gianlucarenzi/stalker/hw/AmigaKeyboardAdapters/A500-Internal/images/A500MPU-Adapter.png

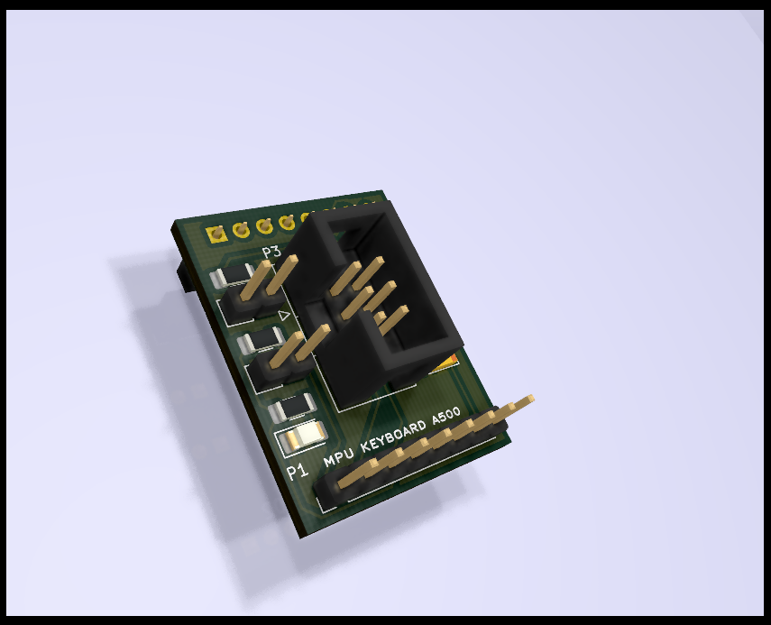
hw/AmigaKeyboardAdapters/A500-Internal/images/A500MPU-Adapter.png
