gianlucarenzi/stalker/hw/AmigaKeyboardAdapters/A600-Internal/images/A600MPU-Adapter-B.png

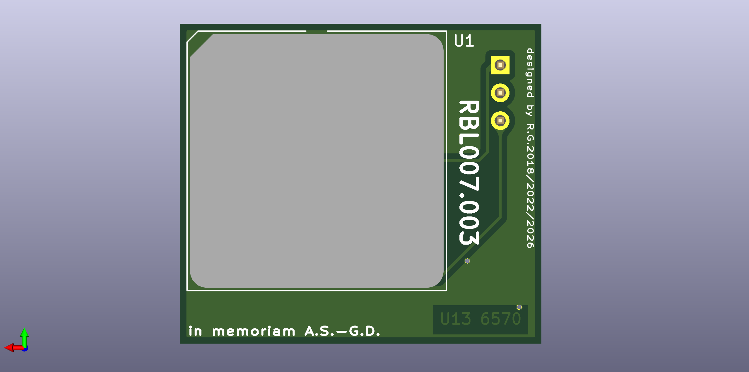
hw/AmigaKeyboardAdapters/A600-Internal/images/A600MPU-Adapter-B.png
