gianlucarenzi/stalker/hw/AmigaKeyboardAdapters/A600-Internal/images/A600MPU-Adapter-F.png

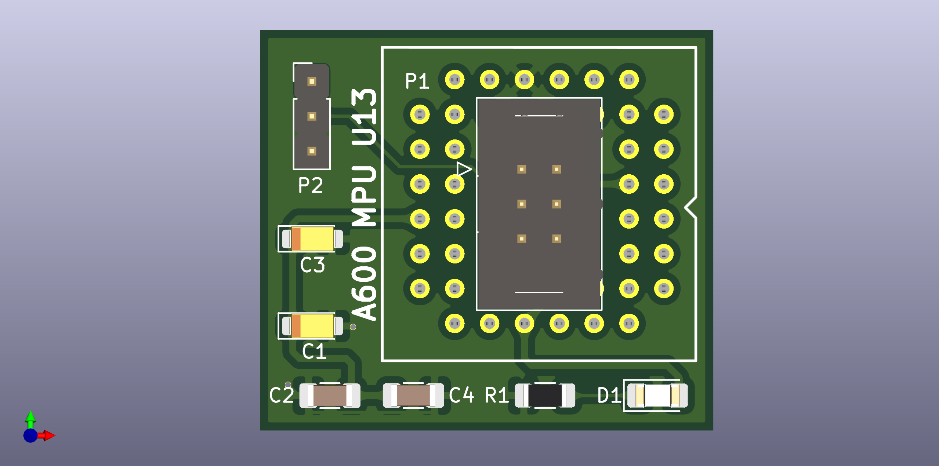
hw/AmigaKeyboardAdapters/A600-Internal/images/A600MPU-Adapter-F.png
