gianlucarenzi/stalker/hw/AmigaKeyboardAdapters/A1200-Internal/A1200MPU-Adapter-b.png

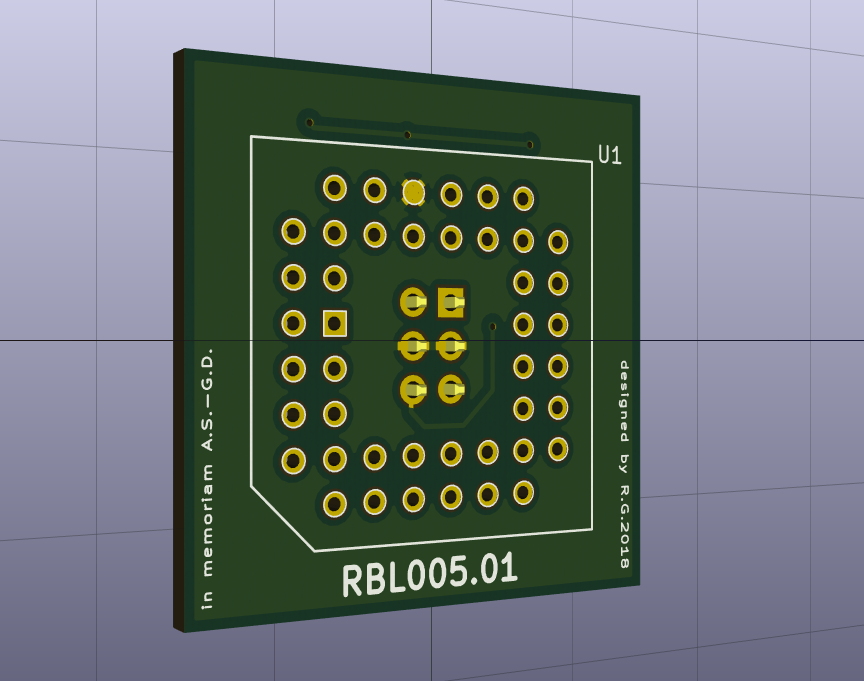
hw/AmigaKeyboardAdapters/A1200-Internal/A1200MPU-Adapter-b.png
