gianlucarenzi/stalker/hw/AmigaKeyboardAdapters/A1200-Internal/A1200MPU-Adapter-f.png

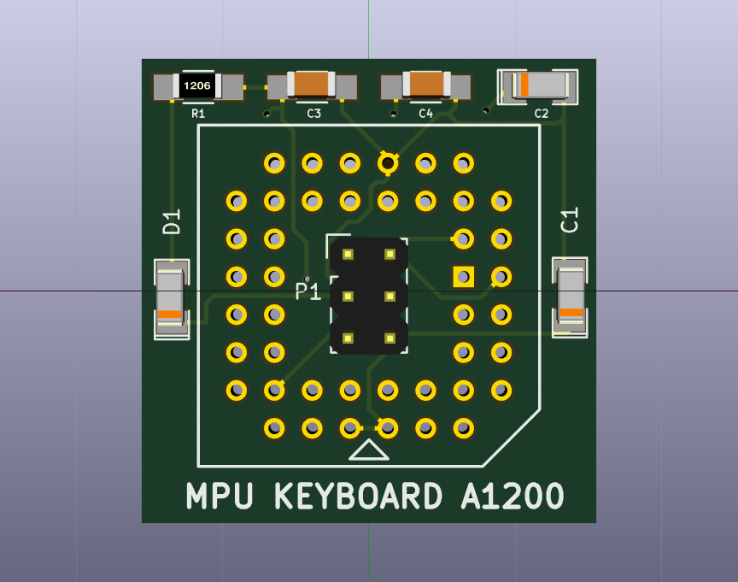
hw/AmigaKeyboardAdapters/A1200-Internal/A1200MPU-Adapter-f.png
