gianlucarenzi/stalker/timing_flow.png

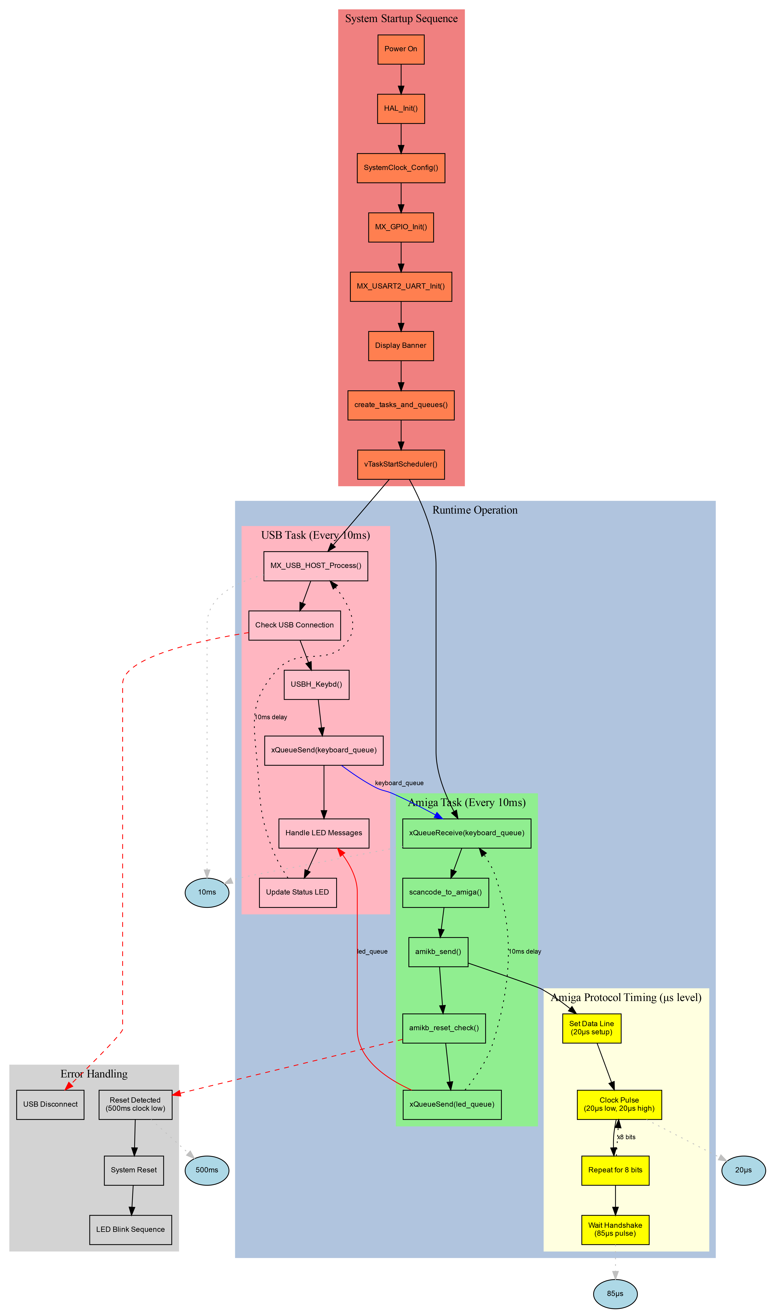
timing_flow.png
