gianlucarenzi/stalker/hw/AmigaKeyboardAdapters/StandAlone-Adapter/production/StandAlone-Adapter.ods

Id | Designator | Package | Quantity | Designation | Codice componente | Codice produttore | Descrizione
1 | U3 | LQFP-64_10x10mm_Pitch0.5mm | 1 | STM32F401RBTx | 497-18782-1-ND | STM32F401RBT6 | IC MCU 32BIT 128KB FLASH 64LQFP
2 | H4,H3,H2,H1 | 1pin | 4 | CONN_01X01 | LM1117MP-3.3/NOPBCT-ND | LM1117MP-3.3/NOPB | IC REG LINEAR 3.3V 800MA SOT223
3 | U1 | SOT-223 | 1 | AZ1117-3.3 | BSS138CT-ND | BSS138 | MOSFET N-CH 50V 220MA SOT-23
4 | TP1 | SolderWirePad_single_0-8mmDrill | 1 | GND | AE10381-ND | A-2004-3-4-LP-N-R | CONN MOD JACK 4P4C R/A UNSHLD
5 | Q3,Q2,Q1 | SOT-23 | 3 | BSS138 | ED2989-ND | USB-A1HSW6 | CONN RCPT TYPEA 4POS R/A
6 | J1 | RJ10-RECEPTACLE-Assmann-ASS-2004-3-4-LP-N-R | 1 | RJ10 | 478-1657-1-ND | TAJA106M010RNJ | CAP TANT 10UF 20% 10V 1206
7 | D1,D2,D3,D4 | LED_1206 | 4 | LED | 399-3692-1-ND | T491A226M010AT | CAP TANT 22UF 20% 10V 1206
8 | R1,R2,R6,R13 | R_1206_HandSoldering | 4 | 1.5K | 720-1803-1-ND | VJ1206Y104KXJPW1BC | CAP CER 0.1UF 16V X7R 1206
9 | R3 | R_1206_HandSoldering | 1 | 22K | 399-12968-1-ND | C1206C475K8NACAUTO | CAP CER 4.7UF 10V X8L 1206
10 | R4,R5,R7,R8,R9,R10,R11,R12,R14,R15 | R_1206_HandSoldering | 10 | 10K | P1.5KECT-ND | ERJ-8GEYJ152V | RES SMD 1.5K OHM 5% 1/4W 1206
11 | USB1 | USB_A_UP | 1 | CONN_01x04 | 541-4201-1-ND | CRCW120610K0JNEAC | RES SMD 10K OHM 5% 1/4W 1206
12 | XT1 | Crystal_HC49-4H_Vertical_3D | 1 | 8Mhz | RMCF1206JT22K0CT-ND | RMCF1206JT22K0 | RES 22K OHM 5% 1/4W 1206
13 | C6,C7,C8,C9,C3,C10,C12,C14 | C_1206_HandSoldering | 8 | 100n | 160-1166-1-ND | LTST-C150AKT | LED AMBER CLEAR SMD
14 | C5,C4 | C_1206_HandSoldering | 2 | 20p | 160-1643-1-ND | LTST-C150TBKT | LED BLUE CLEAR 1206 SMD
15 | SWDIO/CLK1,POWER1 | Pin_Header_Angled_1x04 | 2 | CONN_01X04 | 311-12ERCT-ND | RC1206JR-0712RL | RES SMD 12 OHM 5% 1/4W 1206
16 | DEBUG1,BOOT1,BOOT0 | Pin_Header_Straight_1x03 | 3 | CONN_01X03 | 631-1100-ND | FC4STCBMF8.0-BAG200 | CRYSTAL 8.0000MHZ 20PF T/H
17 | TP1/1,USB_ID1,P1,EN1 | Pin_Header_Straight_1x02 | 4 | CONN_01X02 | 1276-1661-1-ND | CL05C200JB5NNNC | CAP CER 20PF 50V C0G/NP0 0402
18 | RESET1 | SW_SPST_FSMSM_3D | 1 | SW_PUSH | 732-5394-ND | 61200621621 | CONN HEADER VERT 6POS 2.54MM
19 | AMIGA_KEYBOARD1 | Pin_Header_Angled_1x05 | 1 | CONN_01X05 | 609-3288-ND | 68001-420HLF | CONN HEADER VERT 20POS 2.54MM
20 | J2 | IDC-Header_2x03_P2.54mm_Vertical | 1 | Conn_02x03_Odd_Even | 609-3325-ND | 68016-220HLF | CONN HEADER R/A 20POS 2.54MM
21 | C13 | C_1206_HandSoldering | 1 | 4.7u | 450-1140-ND | FSMSM | SWITCH TACTILE SPST-NO 0.05A 24V
22 | R16,R17 | R_1206_HandSoldering | 2 | 12ohm
23 | C1,C11 | TantalC_SizeA_EIA-3216_HandSoldering | 2 | 10u
24 | C2 | TantalC_SizeA_EIA-3216_HandSoldering | 1 | 22u
25 | WBLOGO | amigaWorkBench1 | 1 | LOGO
26 | AMIGALOGO | amigaLogo_BW_31x12mm | 1 | LOGO
27 | GNULOGO | Symbol_GNU-GPL_SilkScreen_Small | 1 | Symbol_GNU-GPL_CopperTop_Small
