gianlucarenzi/stalker/src/amiga.c

/**
 * Amiga housekeeping as MPU.
 * Written by Gianluca Renzi R.G.
 * (C) Copyright 2019/2025 by Gianluca Renzi (RetroBitLab Tech Guy)
 * 
 * //
 * // SPDX-License-Identifier: LGPL-3.0-or-later
 *
 * License for this code: LGPLv3
 * Please refer to this license at GNU Web Site
 * https://www.gnu.org/licenses/lgpl-3.0.html
 * 
 **/
#include <string.h>
#include <stdlib.h>
#include <stdbool.h>
#include "main.h"
#include "amiga.h"
#include "debug.h"
#include "cmsis_os.h"
#include "usb_hid_keys.h"
#include "led_manager_task.h"
#include "amiga_task.h"
#include "delay_us.h"
#include "eeprom_task.h"

extern volatile reset_keypress_mode_t current_mode; // Defined in main.c

static int debuglevel = DBG_INFO;

/* KEY definitions moved to usb_hid_keys.h */


#define KEYCODE_TAB_SIZE      122

static const uint8_t scancodeamiga[KEYCODE_TAB_SIZE][2] =
{
 	// SCANCODE USB to AMIGA
 	// --------------------------------------------------------------
 	// Need the real scancode by testing all keys on a real keyboard.
 	// --------------------------------------------------------------
 	// Keycodes from: https://wiki.amigaos.net/wiki/Keymap_Library
 	// --------------------------------------------------------------
	{KEY_GRAVE_ACCENT_AND_TILDE, 0x00 }, // ~
	{KEY_1_EXCLAMATION_MARK,     0x01 }, // 1!
	{KEY_2_AT,                   0x02 }, // 2@
	{KEY_3_NUMBER_SIGN,          0x03 }, // 3#
	{KEY_4_DOLLAR,               0x04 }, // 4$
	{KEY_5_PERCENT,              0x05 }, // 5%
	{KEY_6_CARET,                0x06 }, // 6^
	{KEY_7_AMPERSAND,            0x07 }, // 7&
	{KEY_8_ASTERISK,             0x08 }, // 8*
	{KEY_9_OPARENTHESIS,         0x09 }, // 9(
	{KEY_0_CPARENTHESIS,         0x0A }, // 0)
	{KEY_MINUS_UNDERSCORE,       0x0B }, // -_
	{KEY_EQUAL_PLUS,             0x0C }, // +=
	{KEY_BACKSLASH_VERTICAL_BAR, 0x0D }, // |
	{KEY_INTERNATIONAL3,         0x0E }, // Intl 3 Yen
	{KEY_KEYPAD_0_INSERT,        0x0F }, // NUM 0
	{KEY_Q,                      0x10 }, // Q
	{KEY_W,                      0x11 }, // W
	{KEY_E,                      0x12 }, // E
	{KEY_R,                      0x13 }, // R
	{KEY_T,                      0x14 }, // T
	{KEY_Y,                      0x15 }, // Y
	{KEY_U,                      0x16 }, // U
	{KEY_I,                      0x17 }, // I
	{KEY_O,                      0x18 }, // O
	{KEY_P,                      0x19 }, // P
	{KEY_OBRACKET_AND_OBRACE,    0x1A }, // [{
	{KEY_CBRACKET_AND_CBRACE,    0x1B }, // ]}
	{KEY_INTERNATIONAL5,         0x1C }, // undefined Intl 5
	{KEY_KEYPAD_1_END,           0x1D }, // NUM 1
	{KEY_KEYPAD_2_DOWN_ARROW,    0x1E }, // NUM 2
	{KEY_KEYPAD_3_PAGEDN,        0x1F }, // NUM 3
	{KEY_A,                      0x20 }, // A
	{KEY_S,                      0x21 }, // S
	{KEY_D,                      0x22 }, // D
	{KEY_F,                      0x23 }, // F
	{KEY_G,                      0x24 }, // G
	{KEY_H,                      0x25 }, // H
	{KEY_J,                      0x26 }, // J
	{KEY_K,                      0x27 }, // K
	{KEY_L,                      0x28 }, // L
	{KEY_SEMICOLON_COLON,        0x29 }, // :;
	{KEY_SINGLE_AND_DOUBLE_QUOTE,0x2A }, // "'
	{KEY_INTERNATIONAL1,         0x2B }, // undefined Intl 1
	{KEY_INTERNATIONAL4,         0x2C }, // undefined Intl 4
	{KEY_KEYPAD_4_LEFT_ARROW,    0x2D }, // NUM 4
	{KEY_KEYPAD_5,               0x2E }, // NUM 5
	{KEY_KEYPAD_6_RIGHT_ARROW,   0x2F }, // NUM 6
	{KEY_INTERNATIONAL2,         0x30 }, // <SHIFT> international? Intl 2
	{KEY_Z,                      0x31 }, // Z
	{KEY_X,                      0x32 }, // X
	{KEY_C,                      0x33 }, // C
	{KEY_V,                      0x34 }, // V
	{KEY_B,                      0x35 }, // B
	{KEY_N,                      0x36 }, // N
	{KEY_M,                      0x37 }, // M
	{KEY_COMMA_AND_LESS,         0x38 }, // <,
	{KEY_DOT_GREATER,            0x39 }, // >.
	{KEY_SLASH_QUESTION,         0x3A }, // ?/
	{KEY_INTERNATIONAL6,         0x3B }, // undefined Intl 6
	{KEY_KEYPAD_DECIMAL_SEPARATOR_DELETE, 0x3C }, // KEYPAD '.'
	{KEY_KEYPAD_7_HOME,          0x3D }, // NUM 7
	{KEY_KEYPAD_8_UP_ARROW,      0x3E }, // NUM 8
	{KEY_KEYPAD_9_PAGEUP,        0x3F }, // NUM 9
	{KEY_SPACEBAR,               0x40 }, // SPACE
	{KEY_BACKSPACE,              0x41 }, // BACKSPACE
	{KEY_TAB,                    0x42 }, // TAB
	{KEY_ENTER,                  0x43 }, // ENTER
	{KEY_RETURN,                 0x43 }, // RETURN
	{KEY_KEYPAD_ENTER,           0x44 }, // NUM Enter
	{KEY_ESCAPE,                 0x45 }, // ESC
	{KEY_DELETE,                 0x46 }, // DEL
	{KEY_INSERT,                 0x47 }, // INS (usually undefined)
	{KEY_PAGEUP,                 0x48 }, // PAGEUP (usually undefined)
	{KEY_PAGEDOWN,               0x49 }, // PAGEDOWN (usually undefined)
	{KEY_KEYPAD_MINUS,           0x4A }, // NUM -
	{KEY_F11,                    0x4B }, // F11
	{KEY_UPARROW,                0x4C }, // CURSOR U
	{KEY_DOWNARROW,              0x4D }, // CURSOR D
	{KEY_RIGHTARROW,             0x4E }, // CURSOR R
	{KEY_LEFTARROW,              0x4F }, // CURSOR L
	{KEY_F1,                     0x50 }, // F1
	{KEY_F2,                     0x51 }, // F2
	{KEY_F3,                     0x52 }, // F3
	{KEY_F4,                     0x53 }, // F4
	{KEY_F5,                     0x54 }, // F5
	{KEY_F6,                     0x55 }, // F6
	{KEY_F7,                     0x56 }, // F7
	{KEY_F8,                     0x57 }, // F8
	{KEY_F9,                     0x58 }, // F9
	{KEY_F10,                    0x59 }, // F10
	{KEY_KEYPAD_OPARENTHESIS,    0x5A }, // NUM (
	{KEY_KEYPAD_CPARENTHESIS,    0x5B }, // NUM )
	{KEY_KEYPAD_SLASH,           0x5C }, // /
	{KEY_KEYPAD_ASTERIKS,        0x5D }, // NUM *
	{KEY_KEYPAD_PLUS,            0x5E }, // NUM +
	{KEY_HELP,                   0x5F }, // HELP
	{KEY_SCROLL_LOCK,            0x5F }, // HELP (Mapped to ScrollLock?)
	{KEY_APPLICATION,            0x5F }, // APP - HELP (Mapped to Key Application?)
	{KEY_LEFTSHIFT,              0x60 }, // LSHIFT
	{KEY_RIGHTSHIFT,             0x61 }, // RSHIFT
	{KEY_CAPS_LOCK,              0x62 }, // CAPS
	{KEY_LEFTCONTROL,            0x63 }, // LCTRL
	{KEY_RIGHTCONTROL,           0x63 }, // RCTRL
	{KEY_LEFTALT,                0x64 }, // LALT
	{KEY_RIGHTALT,               0x65 }, // RALT
	{KEY_LEFT_GUI,               0x66 }, // LWIN
	{KEY_RIGHT_GUI,              0x67 }, // RWIN
	{KEY_LMOUSE_BUTTON,          0x68 }, // LMOUSE BUTTON
	{KEY_RMOUSE_BUTTON,          0x69 }, // RMOUSE BUTTON
	{KEY_MMOUSE_BUTTON,          0x6A }, // MMOUSE BUTTON
	{KEY_MENU,                   0x6B }, // MENU, GUI, COMPOSE (mappable to RAmiga in Firmware)
	{KEY_KEYPAD_COMMA,           0x6C }, // Brazil NP . (named "Keypad ," in USB specs)
	{KEY_PRINTSCREEN,            0x6D }, // PrintScreen/SysReq (mappable to Help in Firmware)
	{KEY_SYSREQ,                 0x6E }, // BREAK
	{KEY_F12,                    0x6F }, // F12
	{KEY_HOME,                   0x70 }, // HOME
	{KEY_END1,                   0x71 }, // END
	{KEY_STOP,                   0x72 }, // STOP/CD32 Blue Stop, CDTV Stop, Port 0 Blue
	{KEY_PAUSE,                  0x73 }, // Play/Pause CD32 Grey Play/Pause CDTV Play/Pause Port 0 Blue
	{KEY_VOLUME_UP,              0x74 }, // Prev Track CDTV << REV
	{KEY_VOLUME_DOWN,            0x75 }, // Next Track CDTV >> FF
};

static const uint8_t asciiscancode[KEYCODE_TAB_SIZE][2] =
{
	{KEY_GRAVE_ACCENT_AND_TILDE, '~' }, // ~
	{KEY_1_EXCLAMATION_MARK,     '!' }, // 1!
	{KEY_2_AT,                   '@' }, // 2@
	{KEY_3_NUMBER_SIGN,          '#' }, // 3#
	{KEY_4_DOLLAR,               '$' }, // 4$
	{KEY_5_PERCENT,              '%' }, // 5%
	{KEY_6_CARET,                '^' }, // 6^
	{KEY_7_AMPERSAND,            '&' }, // 7&
	{KEY_8_ASTERISK,             '*' }, // 8*
	{KEY_9_OPARENTHESIS,         '(' }, // 9(
	{KEY_0_CPARENTHESIS,         ')' }, // 0)
	{KEY_MINUS_UNDERSCORE,       '-' }, // -_
	{KEY_EQUAL_PLUS,             '+' }, // +=
	{KEY_BACKSLASH_VERTICAL_BAR, '|' }, // |
	{KEY_NONE,                   '-' }, // @
	{KEY_KEYPAD_0_INSERT,        '0' }, // NUM 0
	{KEY_Q,                      'Q' }, // Q
	{KEY_W,                      'W' }, // W
	{KEY_E,                      'E' }, // E
	{KEY_R,                      'R' }, // R
	{KEY_T,                      'T' }, // T
	{KEY_Y,                      'Y' }, // Y
	{KEY_U,                      'U' }, // U
	{KEY_I,                      'I' }, // I
	{KEY_O,                      'O' }, // O
	{KEY_P,                      'P' }, // P
	{KEY_OBRACKET_AND_OBRACE,    '{' }, // [{
	{KEY_CBRACKET_AND_CBRACE,    '}' }, // ]}
	{KEY_SPACEBAR,               ' ' }, // SPACE
	{KEY_KEYPAD_1_END,           '1' }, // NUM 1
	{KEY_KEYPAD_2_DOWN_ARROW,    '2' }, // NUM 2
	{KEY_KEYPAD_3_PAGEDN,        '3' }, // NUM 3
	{KEY_A,                      'A' }, // A
	{KEY_S,                      'S' }, // S
	{KEY_D,                      'D' }, // D
	{KEY_F,                      'F' }, // F
	{KEY_G,                      'G' }, // G
	{KEY_H,                      'H' }, // H
	{KEY_J,                      'J' }, // J
	{KEY_K,                      'K' }, // K
	{KEY_L,                      'L' }, // L
	{KEY_SEMICOLON_COLON,        ':' }, // :;
	{KEY_SINGLE_AND_DOUBLE_QUOTE,'"' }, // "'
	{KEY_ENTER,                  '\n'}, // <RET> international?
	{KEY_KEYPAD_4_LEFT_ARROW,    '4' }, // NUM 4
	{KEY_KEYPAD_5,               '5' }, // NUM 5
	{KEY_KEYPAD_6_RIGHT_ARROW,   '6' }, // NUM 6
	{KEY_INTERNATIONAL2,         '-' }, // <SHIFT> international?
	{KEY_Z,                      'Z' }, // Z
	{KEY_X,                      'X' }, // X
	{KEY_C,                      'C' }, // C
	{KEY_V,                      'V' }, // V
	{KEY_B,                      'B' }, // B
	{KEY_N,                      'N' }, // N
	{KEY_M,                      'M' }, // M
	{KEY_COMMA_AND_LESS,         '<' }, // <,
	{KEY_KEYPAD_COMMA,           ',' }, // NUM ,
	{KEY_DOT_GREATER,            '>' }, // >.
	{KEY_SLASH_QUESTION,         '?' }, // ?/
	{KEY_KEYPAD_7_HOME,          '7' }, // NUM 7
	{KEY_KEYPAD_8_UP_ARROW,      '8' }, // NUM 8
	{KEY_KEYPAD_9_PAGEUP,        '9' }, // NUM 9
	{KEY_SPACEBAR,               ' ' }, // SPACE
	{KEY_BACKSPACE,              '\r'}, // BACKSPACE
	{KEY_TAB,                    '\t'}, // TAB
	{KEY_KEYPAD_ENTER,           '\n'}, // ENTER
	{KEY_RETURN,                 '\n'}, // RETURN
	{KEY_ESCAPE,                 '-' }, // ESC
	{KEY_DELETE,                 '\r'}, // DEL
	{KEY_KEYPAD_MINUS,           '-' }, // NUM -
	{KEY_KEYPAD_SLASH,           '/' }, // /
	{KEY_KEYPAD_ASTERIKS,        '*' }, // NUM *
	{KEY_KEYPAD_PLUS,            '+' }, // NUM +
	{KEY_HELP,                   'h' }, // HELP
	{KEY_APPLICATION,            'h' }, // APP - HELP
	{KEY_NONE,                   '(' }, // (
	{KEY_NONE,                   ')' }, // )
	{KEY_NONE,                   ' ' }, // SPARE
	{KEY_NONE,                   ' ' }, // SPARE
	{KEY_NONE,                   ' ' }, // SPARE
	{KEY_NONE,                   ' ' }, // SPARE
	{KEY_NONE,                   ' ' }, // SPARE
	{KEY_NONE,                   ' ' }, // SPARE
	{KEY_UPARROW,                ' ' }, // CURSOR U
	{KEY_DOWNARROW,              ' ' }, // CURSOR D
	{KEY_RIGHTARROW,             ' ' }, // CURSOR R
	{KEY_LEFTARROW,              ' ' }, // CURSOR L
	{KEY_F1,                     ' ' }, // F1
	{KEY_F2,                     ' ' }, // F2
	{KEY_F3,                     ' ' }, // F3
	{KEY_F4,                     ' ' }, // F4
	{KEY_F5,                     ' ' }, // F5
	{KEY_F6,                     ' ' }, // F6
	{KEY_F7,                     ' ' }, // F7
	{KEY_F8,                     ' ' }, // F8
	{KEY_F9,                     ' ' }, // F9
	{KEY_F10,                    ' ' }, // F10
	{KEY_LEFTSHIFT,              ' ' }, // LSHIFT
	{KEY_RIGHTSHIFT,             ' ' }, // RSHIFT
	{KEY_LOCKING_CAPS_LOCK,      ' ' }, // CAPS
	{KEY_LEFTCONTROL,            ' ' }, // LCTRL
	{KEY_LEFTALT,                ' ' }, // LALT
	{KEY_RIGHTALT,               ' ' }, // RALT
	{KEY_LEFT_GUI,               ' ' }, // LWIN
	{KEY_RIGHT_GUI,              ' ' }, // RWIN
	{KEY_NONE,                   ' ' }, // STUB
	{KEY_NONE,                   ' ' }, // STUB
	{KEY_NONE,                   ' ' }, // STUB
	{KEY_NONE,                   ' ' }, // STUB
	{KEY_NONE,                   ' ' }, // STUB
	{KEY_NONE,                   ' ' }, // STUB
	{KEY_NONE,                   ' ' }, // STUB
	{KEY_NONE,                   ' ' }, // STUB
	{KEY_NONE,                   ' ' }, // STUB
	{KEY_NONE,                   ' ' }, // STUB
	{KEY_NONE,                   ' ' }, // STUB
	{KEY_NONE,                   ' ' }, // STUB
	{KEY_NONE,                   ' ' }, // STUB
	{KEY_NONE,                   ' ' }, // STUB
	{KEY_NONE,                   ' ' }, // STUB
	{KEY_NONE,                   ' ' }, // STUB
	{KEY_NONE,                   ' ' }, // STUB
};


/**
	The keyboard transmits 8-bit data words serially to the main unit. Before
	the transmission starts, both KCLK and KDAT are high.  The keyboard starts
	the transmission by putting out the first data bit (on KDAT), followed by
	a pulse on KCLK (low then high); then it puts out the second data bit and
	pulses KCLK until all eight data bits have been sent.  After the end of
	the last KCLK pulse, the keyboard pulls KDAT high again.

	When the computer has received the eighth bit, it must pulse KDAT low for
	at least 1 (one) microsecond, as a handshake signal to the keyboard.  The
	handshake detection on the keyboard end will typically use a hardware
	latch.  The keyboard must be able to detect pulses greater than or equal
	to 1 microsecond.  Software MUST pulse the line low for 85 microseconds to
	ensure compatibility with all keyboard models.

	All codes transmitted to the computer are rotated one bit before
	transmission.  The transmitted order is therefore 6-5-4-3-2-1-0-7. The
	reason for this is to transmit the  up/down flag  last, in order to cause
	a key-up code to be transmitted in case the keyboard is forced to restore
	 lost sync  (explained in more detail below).

	The KDAT line is active low; that is, a high level (+5V) is interpreted as
	0, and a low level (0V) is interpreted as 1.

				 _____   ___   ___   ___   ___   ___   ___   ___   _________
			KCLK      \_/   \_/   \_/   \_/   \_/   \_/   \_/   \_/
				 ___________________________________________________________
			KDAT    \_____X_____X_____X_____X_____X_____X_____X_____/
					  (6)   (5)   (4)   (3)   (2)   (1)   (0)   (7)

					 First                                     Last
					 sent                                      sent

	The keyboard processor sets the KDAT line about 20 microseconds before it
	pulls KCLK low.  KCLK stays low for about 20 microseconds, then goes high
	again.  The processor waits another 20 microseconds before changing KDAT.

	Therefore, the bit rate during transmission is about 60 microseconds per
	bit, or 17 kbits/sec.
	*
	*
	*
	*
	*
	*
	* Is this LookUpTable needed for translating from ascii to internal keycode?


			Row 5   Row 4   Row 3   Row 2   Row 1   Row 0
	Column    (Bit 7) (Bit 6) (Bit 5) (Bit 4) (Bit 3) (Bit 2)
		   +-------+-------+-------+-------+-------+-------+
	 15    |(spare)|(spare)|(spare)|(spare)|(spare)|(spare)|
	(PD.7) |       |       |       |       |       |       |
		   | (0E)  | (1C)  | (2C)  | (47)  | (48)  | (49)  |
		   +-------+-------+-------+-------+-------+-------+
	 14    |   *   |<SHIFT>| CAPS  |  TAB  |   ~   |  ESC  |
	(PD.6) |note 1 |note 2 | LOCK  |       |   `   |       |
		   | (5D)  | (30)  | (62)  | (42)  | (00)  | (45)  |
		   +-------+-------+-------+-------+-------+-------+
	 13    |   +   |   Z   |   A   |   Q   |   !   |   (   |
	(PD.5) |note 1 |       |       |       |   1   |note 1 |
		   | (5E)  | (31)  | (20)  | (10)  | (01)  | (5A)  |
		   +-------+-------+-------+-------+-------+-------+
	 12    |  9    |   X   |   S   |   W   |   @   |  F1   |
	(PD.4) |note 3 |       |       |       |   2   |       |
		   | (3F)  | (32)  | (21)  | (11)  | (02)  | (50)  |
		   +-------+-------+-------+-------+-------+-------+
	 11    |  6    |   C   |   D   |   E   |   #   |  F2   |
	(PD.3) |note 3 |       |       |       |   3   |       |
		   | (2F)  | (33)  | (22)  | (12)  | (03)  | (51)  |
		   +-------+-------+-------+-------+-------+-------+
	 10    |  3    |   V   |   F   |   R   |   $   |  F3   |
	(PD.2) |note 3 |       |       |       |   4   |       |
		   | (1F)  | (34)  | (23)  | (13)  | (04)  | (52)  |
		   +-------+-------+-------+-------+-------+-------+
	  9    |  .    |   B   |   G   |   T   |   %   |  F4   |
	(PD.1) |note 3 |       |       |       |   5   |       |
		   | (3C)  | (35)  | (24)  | (14)  | (05)  | (53)  |
		   +-------+-------+-------+-------+-------+-------+
	  8    |  8    |   N   |   H   |   Y   |   ^   |  F5   |
	(PD.0) |note 3 |       |       |       |   6   |       |
		   | (3E)  | (36)  | (25)  | (15)  | (06)  | (54)  |
		   +-------+-------+-------+-------+-------+-------+
	  7    |  5    |   M   |   J   |   U   |   &   |   )   |
	(PC.7) |note 3 |       |       |       |   7   |note 1 |
		   | (2E)  | (37)  | (26)  | (16)  | (07)  | (5B)  |
		   +-------+-------+-------+-------+-------+-------+
	  6    |  2    |   <   |   K   |   I   |   *   |  F6   |
	(PC.6) |note 3 |   ,   |       |       |   8   |       |
		   | (1E)  | (38)  | (27)  | (17)  | (08)  | (55)  |
		   +-------+-------+-------+-------+-------+-------+
	  5    | ENTER |   >   |   L   |   O   |   (   |   /   |
	(PC.5) |note 3 |   .   |       |       |   9   |note 1 |
		   | (43)  | (39)  | (28)  | (18)  | (09)  | (5C)  |
		   +-------+-------+-------+-------+-------+-------+
	  4    |  7    |   ?   |   :   |   P   |   )   |  F7   |
	(PC.4) |note 3 |   /   |   ;   |       |   0   |       |
		   | (3D)  | (3A)  | (29)  | (19)  | (0A)  | (56)  |
		   +-------+-------+-------+-------+-------+-------+
	  3    |  4    |(spare)|   "   |   {   |   _   |  F8   |
	(PC.3) |note 3 |       |   '   |   [   |   -   |       |
		   | (2D)  | (3B)  | (2A)  | (1A)  | (0B)  | (57)  |
		   +-------+-------+-------+-------+-------+-------+
	  2    |  1    | SPACE | <RET> |   }   |   +   |  F9   |
	(PC.2) |note 3 |  BAR  |note 2 |   ]   |   =   |       |
		   | (1D)  | (40)  | (2B)  | (1B)  | (0C)  | (58)  |
		   +-------+-------+-------+-------+-------+-------+
	  1    |  0    | BACK  |  DEL  |RETURN |   |   |  F10  |
	(PC.1) |note 3 | SPACE |       |       |   \   |       |
		   | (0F)  | (41)  | (46)  | (44)  | (0D)  | (59)  |
		   +-------+-------+-------+-------+-------+-------+
	  0    |  -    | CURS  | CURS  | CURS  | CURS  | HELP  |
	(PC.0) |note 3 | DOWN  | RIGHT | LEFT  |  UP   |       |
		   | (4A)  | (4D)  | (4E)  | (4F)  | (4C)  | (5F)  |
		   +-------+-------+-------+-------+-------+-------+

	note 1: A500, A2000 and A3000 keyboards only (numeric pad )
	note 2: International keyboards only (these keys are cutouts of the
		   larger key on the US ASCII version.)  The key that generates
		   $30 is cut out of the left Shift key.  Key $2B is cut out of
		   return.  These keys are labeled with country-specific markings.
	note 3: Numeric pad.


	The following table shows which keys are independently readable.  These
	keys never generate ghosts or phantoms.


		(Bit 6) (Bit 5) (Bit 4) (Bit 3) (Bit 2) (Bit 1) (Bit 0)
	   +-------+-------+-------+-------+-------+-------+-------+
	   | LEFT  | LEFT  | LEFT  | CTRL  | RIGHT | RIGHT | RIGHT |
	   | AMIGA | ALT   | SHIFT |       | AMIGA |  ALT  | SHIFT |
	   | (66)  | (64)  | (60)  | (63)  | (67)  | (65)  | (61)  |
	   +-------+-------+-------+-------+-------+-------+-------+

	About Hard Reset.
	-----------------
	Hard Reset happens after  Reset Warning . Valid for all keyboards
	except the Amiga 500.

	The keyboard Hard Resets the Amiga by pulling KCLK low and starting a 500
	millisecond timer.   When one or more of the keys is released and 500
	milliseconds have passed, the keyboard will release KCLK. 500 milliseconds
	is the minimum time KCLK must be held low.  The maximum KCLK time depends
	on how long the user holds the three  reset keys  down.  Circuitry on the
	Amiga motherboard detects the 500 millisecond KCLK pulse.

	After releasing KCLK, the keyboard jumps to its start-up code (internal
	RESET).  This will initialize the keyboard in the same way as cold
	power-on .

 **/

typedef enum {
	DAT_OUTPUT = 0,
	DAT_INPUT,
} kbd_dir;

static unsigned char prev_keycode = 0xff;
static unsigned char capslk = 0;
static unsigned char numlk = 0;
static unsigned char scrolllk = 0;

static void amikb_direction(kbd_dir dir);
led_status_t amikb_send(uint8_t code, int press, int use_OS);

/**
 * @brief  Converts a USB HID scancode to an Amiga scancode.
 * @param  lkey: The USB HID scancode.
 * @retval The corresponding Amiga scancode.
 **/
uint8_t scancode_to_amiga(uint8_t lkey)
{
	uint8_t i = 0, keyvalue = lkey;
	DBG_V("Enter with 0x%02x lkey ScanCode\r\n", lkey);

	for (i = 0; i < KEYCODE_TAB_SIZE; i++)
	{
		DBG_N("SCANCODE: 0x%02x - AMIGA: 0x%02x\r\n",
			scancodeamiga[i][0], scancodeamiga[i][1]);
		if (lkey == scancodeamiga[i][0])
		{
			keyvalue = scancodeamiga[i][1];
			break;
		}
	}

	DBG_V("Exit with: 0x%02x Amiga ScanCode\r\n", keyvalue);
	return keyvalue;
}

/**
 * @brief  Converts an ASCII character to a USB HID scancode.
 * @param  ascii: The ASCII character.
 * @retval The corresponding USB HID scancode.
 **/
uint8_t ascii_to_scancode(uint8_t ascii)
{
	uint8_t i = 0, keyvalue = ascii;
	DBG_V("Enter with '%c' 0x%02x ASCII\r\n", ascii, ascii);

	for (i = 0; i < KEYCODE_TAB_SIZE; i++)
	{
		if (ascii == asciiscancode[i][1])
		{
			keyvalue = asciiscancode[i][0];
			break;
		}
	}

	DBG_V("Exit with: 0x%02x ScanCode\r\n", keyvalue);
	return keyvalue;
}

/**
 * @brief  Initializes the Amiga keyboard.
 * @retval None
 **/
void amikb_startup(int use_OS)
{
	uint8_t AMIGA_INITPOWER = 0xFD; //11111101
	uint8_t AMIGA_TERMPOWER = 0xFE; //11111110

	DBG_V("Enter\r\n");

	// De-assert nRESET for Amiga...
	amikb_reset(use_OS);

	amikb_direction(DAT_OUTPUT); // Default

	if (use_OS)
	{
		osDelay(RESET_TIMEOUT_MS * 2);
	}
	else
	{
		HAL_Delay(RESET_TIMEOUT_MS * 2);              // wait for sync
	}
	amikb_send((uint8_t) AMIGA_INITPOWER, 0, use_OS); // send "initiate power-up"
	udelay(200);
	amikb_send((uint8_t) AMIGA_TERMPOWER, 0, use_OS); // send "terminate power-up"

	DBG_V("Exit\r\n");
}

static int keyboard_is_present = 0;

/**
 * @brief  Sets the keyboard presence status.
 * @param  isready: 1 if the keyboard is present, 0 otherwise.
 * @retval None
 **/
void amikb_ready(int isready)
{
	keyboard_is_present = isready;
}

/**
 * @brief  Initializes the GPIO pins for the Amiga keyboard.
 * @retval None
 **/
void amikb_gpio_init(void)
{
	GPIO_InitTypeDef GPIO_InitStruct;

	DBG_N("Enter\r\n");

	/* GPIO Port C Clock Enable */
	__HAL_RCC_GPIOC_CLK_ENABLE();

	/*Configure GPIO pin Output Level */
	HAL_GPIO_WritePin(GPIOC,
		KBD_CLOCK_Pin |
		KBD_DATA_Pin  |
		KBD_RESET_Pin, GPIO_PIN_SET);

	/*Configure GPIO pins : KBD_CLOCK_Pin KBD_DATA_Pin KBD_RESET_Pin */
	GPIO_InitStruct.Pin = KBD_CLOCK_Pin |KBD_DATA_Pin | KBD_RESET_Pin;
	GPIO_InitStruct.Mode = GPIO_MODE_OUTPUT_PP;
	GPIO_InitStruct.Pull = GPIO_NOPULL;
	GPIO_InitStruct.Speed = GPIO_SPEED_FREQ_LOW;
	HAL_GPIO_Init(GPIOC, &GPIO_InitStruct);

	// Lasciamo l'Amiga in RESET finche' non parte la macchina a stati
	HAL_GPIO_WritePin(GPIOC, KBD_RESET_Pin, GPIO_PIN_RESET); // Clear KBD_RESET pin

	DBG_N("Exit\r\n");
}

/**
 * @brief  Sets the direction of the keyboard data and clock lines.
 * @param  dir: The direction of the lines (DAT_INPUT or DAT_OUTPUT).
 * @retval None
 **/
static void amikb_direction(kbd_dir dir)
{
	GPIO_InitTypeDef GPIO_InitStruct;

	DBG_N("Enter with: %d\r\n", dir);
	/*Configure GPIO KBD_DAT, GPIO KBD_CLOCK as inputs and KBD_RESET as output */
	GPIO_InitStruct.Pin = KBD_CLOCK_Pin |KBD_DATA_Pin;
	GPIO_InitStruct.Speed = GPIO_SPEED_FREQ_LOW;
	switch (dir)
	{
		case DAT_INPUT:
			GPIO_InitStruct.Mode = GPIO_MODE_INPUT;
			GPIO_InitStruct.Pull = GPIO_PULLUP;
			break;

		default:
		case DAT_OUTPUT:
			GPIO_InitStruct.Mode = GPIO_MODE_OUTPUT_PP;
			GPIO_InitStruct.Pull = GPIO_NOPULL;
			break;
	}
	HAL_GPIO_Init(GPIOC, &GPIO_InitStruct);

	/* Now configure KBD_RESET_Pin as output */
	GPIO_InitStruct.Pin = KBD_RESET_Pin;
	GPIO_InitStruct.Mode = GPIO_MODE_OUTPUT_PP;
	GPIO_InitStruct.Pull = GPIO_NOPULL;
	GPIO_InitStruct.Speed = GPIO_SPEED_FREQ_LOW;
	HAL_GPIO_Init(GPIOC, &GPIO_InitStruct);

	DBG_N("Exit\r\n");
}

/**
 * @brief  Sends a keycode to the Amiga.
 * @param  keycode: The Amiga scancode to send.
 * @param  press: 1 if the key is pressed, 0 if it is released.
 * @retval The LED status.
 **/
led_status_t amikb_send(uint8_t keycode, int press, int use_OS)
{
	int i;
	led_status_t rval = NO_LED;

	DBG_V("Amiga Keycode 0x%02x - %s\r\n", keycode, press ? "PRESSED" : "RELEASED");
	if (keycode == 0x62 || keycode == 0x68 || keycode == 0x1c) // Caps Lock, Num Lock or Scroll Lock Pressed or Released
	{
		// caps lock doesn't get a key release event when the key is released
		// but rather when the caps lock is toggled off again
		// But what about num lock?

		switch (keycode)
		{
			case 0x62: // CAPS LOCK LED
				if (!capslk)
				{
					if (press)
					{
						DBG_V("### SEND TURN-ON CAPS LOCK LED. ALL UPPERCASE FROM NOW ###\r\n");
						rval = LED_CAPS_LOCK_ON;
						prev_keycode = 0;
						break;
					}
					else
					{
						DBG_V("### IGNORING RELEASE FOR CAPS LOCK ###\n\r");
						// Toggle for next time press
						capslk = 1;
						prev_keycode = 0;
						return NO_LED;
					}
				}
				else
				{
					if (press)
					{
						DBG_V("### IGNORING PRESS FOR CAPS LOCK. IT WAS ALREADY PRESSED ###\r\n");
						prev_keycode = 0;
						return NO_LED;
					}
					else
					{
						DBG_V("### SEND TURN-OFF CAPS LOCK LED. ALL LOWERCASE FROM NOW ###\r\n");
						capslk = 0;
						rval = LED_CAPS_LOCK_OFF;
						prev_keycode = 0;
						break;
					}
				}
				break;
			case 0x68: // NUM LOCK LED
				if (!numlk)
				{
					if (press)
					{
						DBG_V("### SEND TURN-ON NUM LOCK LED. NUMERIC KEYPAD LOCKED FROM NOW ###\r\n");
						rval = LED_NUM_LOCK_ON;
						prev_keycode = 0;
						break;
					}
					else
					{
						DBG_V("### IGNORING RELEASE FOR NUM LOCK ###\n\r");
						// Toggle for next time press
						numlk = 1;
						prev_keycode = 0;
						return NO_LED;
					}
				}
				else
				{
					if (press)
					{
						DBG_V("### IGNORING PRESS FOR NUM LOCK. IT WAS ALREADY PRESSED ###\r\n");
						prev_keycode = 0;
						return NO_LED;
					}
					else
					{
						DBG_V("### SEND TURN-OFF NUM LOCK LED. NUMERIC KEYPAD UNLOCKED FROM NOW ###\r\n");
						numlk = 0;
						rval = LED_NUM_LOCK_OFF;
						prev_keycode = 0;
						break;
					}
				}
				break;
			case 0x1c: // SCROLL LOCK LED
				if (!scrolllk)
				{
					if (press)
					{
						DBG_V("### SEND TURN-ON SCROLL LOCK LED. SCROLL IS LOCKED FROM NOW ###\r\n");
						rval = LED_SCROLL_LOCK_ON;
						prev_keycode = 0;
						break;
					}
					else
					{
						DBG_V("### IGNORING RELEASE FOR SCROLL LOCK ###\n\r");
						// Toggle for next time press
						scrolllk = 1;
						prev_keycode = 0;
						return NO_LED;
					}
				}
				else
				{
					if (press)
					{
						DBG_V("### IGNORING PRESS FOR SCROLL LOCK. IT WAS ALREADY PRESSED ###\r\n");
						prev_keycode = 0;
						return NO_LED;
					}
					else
					{
						DBG_V("### SEND TURN-OFF SCROLL LOCK LED. SCROLL IS UNLOCKED FROM NOW ###\r\n");
						scrolllk = 0;
						rval = LED_SCROLL_LOCK_OFF;
						prev_keycode = 0;
						break;
					}
				}
				break;
			default:
				{
					DBG_V("NUMLOCK %d - CAPSLOCK %d - SCROLLLOCK %d - PRESSED: %d\r\n",
						numlk, capslk, scrolllk, press);
					return NO_LED;
				}
				break;
		}
	}

	// keycode bit transfer order: 6 5 4 3 2 1 0 7 (7 is pressed flag)
	keycode = (keycode << 1) | (~press & 1);
	if (keycode == prev_keycode)
	{
		DBG_N("NO SENDING THE SAME KEYCODE TWO TIMES IN A ROW\r\n");
		return NO_LED;
	}

	prev_keycode = keycode;

	// Set direction DAT & CLOCK as output to ensure the correct
	// movement of the edges (CLK and DAT)
	amikb_direction(DAT_OUTPUT);

	// make sure we don't pulse the lines while grabbing control
	// by first reinstating the pullups before changing direction
	HAL_GPIO_WritePin(GPIOC, KBD_DATA_Pin, GPIO_PIN_SET); // Normally KBD_DATA pin is HIGH

	// pulse the data line and wait for about 100us
	HAL_GPIO_WritePin(GPIOC, KBD_DATA_Pin, GPIO_PIN_RESET); // KBD_DATA pin is LOW
	udelay(20);
	HAL_GPIO_WritePin(GPIOC, KBD_DATA_Pin, GPIO_PIN_SET); // KBD_DATA pin is HIGH
	udelay(100);

	// Send byte to LED manager for visualization
	extern osMessageQueueId_t ledManagerQueueHandle;
	if (ledManagerQueueHandle != NULL)
	{
		led_manager_message_t led_msg = {
			.command = LED_CMD_BLINK_BYTE,
			.data = keycode,
			.duration_ms = 0
		};
		osMessageQueuePut(ledManagerQueueHandle, &led_msg, 0, 0);
	}

	for (i = 0; i < 8; i++)
	{
		// data line is inverted
		if (keycode & 0x80)
		{
			// a logic 1 is low in hardware
			HAL_GPIO_WritePin(GPIOC, KBD_DATA_Pin, GPIO_PIN_RESET);
		}
		else
		{
			// a logic 0 is high in hardware
			HAL_GPIO_WritePin(GPIOC, KBD_DATA_Pin, GPIO_PIN_SET);
		}
		keycode <<= 1;
		udelay(20);
		/* pulse the clock */
		HAL_GPIO_WritePin(GPIOC, KBD_CLOCK_Pin, GPIO_PIN_RESET); // Clear KBD_CLOCK pin
		udelay(20);
		HAL_GPIO_WritePin(GPIOC, KBD_CLOCK_Pin, GPIO_PIN_SET); // Set KBD_CLOCK pin
		udelay(20);
	}

	HAL_GPIO_WritePin(GPIOC, KBD_DATA_Pin, GPIO_PIN_SET); // Set KBD_DATA pin

	DBG_V("DATA AND CLOCK AS INPUTS. WAITING FOR SYNC FROM CPU\r\n");
	amikb_direction( DAT_INPUT );

#ifdef REAL_AMIKEYBOARD_SYNC
#warning "USING REAL AMIGA MOTHERBOARD HANDSHAKE"
	// Now the Amiga CPU send the sync signal lowering the KBD_DAT signal atleast 1 microsecond
	{
		if (keyboard_is_present)
		{
			int hshakepulse_ms = 143;
			int sync;
			for (;;)
			{
				sync = HAL_GPIO_ReadPin(GPIOC, KBD_DATA_Pin);
				if (sync == 0 || hshakepulse_ms == 0)
					break;
				hshakepulse_ms--;
				if (use_OS)
				{
					osDelay(1);
				}
				else
				{
					HAL_Delay(1);
				}
			}
			if (hshakepulse_ms == 0)
			{
				DBG_E("CPU KEYBOARD SYNC not received within 143msec!\r\n");
			}
		}
	}
#else
#warning "USING TIMED HANDSHAKE"
	if (use_OS)
	{
		osDelay(5); // handshake wait 5msec
	}
	else
	{
		HAL_Delay(5); // handshake wait 500msec
	}
#endif
	// The following instructions should be useless as the port has been configured as input few
	// lines above... :-/
	HAL_GPIO_WritePin(GPIOC, KBD_DATA_Pin,  GPIO_PIN_SET); // Set KBD_DATA pin
	HAL_GPIO_WritePin(GPIOC, KBD_CLOCK_Pin, GPIO_PIN_SET); // Set KBD_CLOCK pin
	DBG_N("Exit: %d\r\n", rval);
	return rval;
}

/**
 * @brief  Resets the Amiga keyboard.
 * @retval None
 **/
void amikb_reset(int use_OS)
{
	amikb_direction(DAT_OUTPUT);
	DBG_V("Enter\r\n");
	HAL_GPIO_WritePin(GPIOC, KBD_RESET_Pin, GPIO_PIN_RESET); // Clear KBD_RESET pin
	HAL_GPIO_WritePin(GPIOC, KBD_CLOCK_Pin, GPIO_PIN_RESET); // Clear KBD_CLOCK pin
	if (use_OS)
	{
		osDelay(RESET_TIMEOUT_MS + 50);
	}
	else
	{
		HAL_Delay(RESET_TIMEOUT_MS + 50);
	}

	HAL_GPIO_WritePin(GPIOC, KBD_RESET_Pin, GPIO_PIN_SET);   // Set KBD_RESET pin
	HAL_GPIO_WritePin(GPIOC, KBD_CLOCK_Pin, GPIO_PIN_SET);   // Set KBD_CLOCK pin
	prev_keycode = 0xff;
	capslk = 0;
	numlk = 0;
	scrolllk = 0;
	DBG_V("Exit\r\n");
}

/**
 * @brief  Checks if the Amiga keyboard is being reset.
 *         The caller should be take note of the level and timings.
 *         Amiga Reset is low only if it is longer than 500msec.
 *         i.e. RESET_TIMER calls.
 * @retval true if the keyboard is being reset, false otherwise.
 **/
#define RESET_TIMER  (50)

bool amikb_reset_check(void)
{
	bool is_low;
	DBG_N("Enter\r\n");
	amikb_direction( DAT_INPUT );
	is_low = HAL_GPIO_ReadPin(GPIOC, KBD_CLOCK_Pin) == GPIO_PIN_RESET ? true : false;
	DBG_N("KBD_CLOCK is %s\r\n", is_low == false ? "LOW" : "HIGH");
	return is_low;
}

#define OK_RESET	3 /* 3 special keys to have a KBRESET */
/*
 * We can have 2 combinations for RESET:
 * 
 * LCTRL + LGUI + RGUI ---> Amiga Standard
 * LCRTL + LALT + DEL  ---> PC Standard
 * 
 * ...and any other combination of those keys!
 * 
 **/
/**
 * @brief  Processes a keyboard code from the USB host.
 * @param  data: A pointer to the keyboard code structure.
 * @retval The LED status.
 **/
led_status_t amikb_process(keyboard_code_t *data, int use_OS)
{
	int i;
	led_status_t rval = NO_LED; /* 0 means no USB interaction such as leds, ... */
	static keyboard_code_t prevkeycode = {
		.lctrl          = 0,
		.lctrlpressed   = 0,
		.lshift         = 0,
		.lshiftpressed  = 0,
		.lalt           = 0,
		.laltpressed    = 0,
		.lgui           = 0,
		.lguipressed    = 0,
		.rctrl          = 0,
		.rctrlpressed   = 0,
		.rshift         = 0,
		.rshiftpressed  = 0,
		.ralt           = 0,
		.raltpressed    = 0,
		.rgui           = 0,
		.rguipressed    = 0,
		.keys[0]        = 0,
		.keyspressed[0] = 0,
		.keys[1]        = 0,
		.keyspressed[1] = 0,
		.keys[2]        = 0,
		.keyspressed[2] = 0,
		.keys[3]        = 0,
		.keyspressed[3] = 0,
		.keys[4]        = 0,
		.keyspressed[4] = 0,
		.keys[5]        = 0,
		.keyspressed[5] = 0,
	};

	DBG_N("Enter with use_OS: %d\r\n", use_OS);

	// ----------------------------------------------- LEFT

	// LEFT SHIFT
	if (prevkeycode.lshift != data->lshift)
	{
		prevkeycode.lshift = data->lshift;
		if (data->lshift == 1)
			prevkeycode.lshiftpressed = 1;
		else
			prevkeycode.lshiftpressed = 0;
		DBG_V("LEFT KEYSHIFT %s\r\n",
			prevkeycode.lshiftpressed == 1 ? "PRESSED" : "RELEASED");
		rval |= amikb_send(scancode_to_amiga(KEY_LEFTSHIFT), prevkeycode.lshiftpressed, use_OS);
	}

	// LEFT ALT
	if (prevkeycode.lalt != data->lalt)
	{
		prevkeycode.lalt = data->lalt;
		if (data->lalt == 1)
			prevkeycode.laltpressed = 1;
		else
			prevkeycode.laltpressed = 0;
		DBG_V("LEFT KEYALT %s\r\n",
			prevkeycode.laltpressed == 1 ? "PRESSED" : "RELEASED");
		rval |= amikb_send(scancode_to_amiga(KEY_LEFTALT), prevkeycode.laltpressed, use_OS);
	}

	// LEFT CTRL
	if (prevkeycode.lctrl != data->lctrl)
	{
		prevkeycode.lctrl = data->lctrl;
		if (data->lctrl == 1)
			prevkeycode.lctrlpressed = 1;
		else
			prevkeycode.lctrlpressed = 0;
		DBG_V("LEFT KEYCTRL %s\r\n",
			prevkeycode.lctrlpressed == 1 ? "PRESSED" : "RELEASED");
		rval |= amikb_send(scancode_to_amiga(KEY_LEFTCONTROL), prevkeycode.lctrlpressed, use_OS);
	}

	// LEFT GUI
	if (prevkeycode.lgui != data->lgui)
	{
		prevkeycode.lgui = data->lgui;
		if (data->lgui == 1)
			prevkeycode.lguipressed = 1;
		else
			prevkeycode.lguipressed = 0;
		DBG_V("LEFT KEYGUI %s\r\n",
			prevkeycode.lguipressed == 1 ? "PRESSED" : "RELEASED");
		rval |= amikb_send(scancode_to_amiga(KEY_LEFT_GUI), prevkeycode.lguipressed, use_OS);
	}

	// ----------------------------------------------- RIGHT
	// RIGHT SHIFT
	if (prevkeycode.rshift != data->rshift)
	{
		prevkeycode.rshift = data->rshift;
		if (data->rshift == 1)
			prevkeycode.rshiftpressed = 1;
		else
			prevkeycode.rshiftpressed = 0;
		DBG_V("RIGHT KEYSHIFT %s\r\n",
			prevkeycode.rshiftpressed == 1 ? "PRESSED" : "RELEASED");
		rval |= amikb_send(scancode_to_amiga(KEY_RIGHTSHIFT), prevkeycode.rshiftpressed, use_OS);
	}

	// RIGHT ALT
	if (prevkeycode.ralt != data->ralt)
	{
		prevkeycode.ralt = data->ralt;
		if (data->ralt == 1)
			prevkeycode.raltpressed = 1;
		else
			prevkeycode.raltpressed = 0;
		DBG_V("RIGHT KEYALT %s\r\n",
			prevkeycode.raltpressed == 1 ? "PRESSED" : "RELEASED");
		rval |= amikb_send(scancode_to_amiga(KEY_RIGHTALT), prevkeycode.raltpressed, use_OS);
	}

	// RIGHT CTRL
	if (prevkeycode.rctrl != data->rctrl)
	{
		prevkeycode.rctrl = data->rctrl;
		if (data->rctrl == 1)
			prevkeycode.rctrlpressed = 1;
		else
			prevkeycode.rctrlpressed = 0;
		DBG_V("RIGHT KEYCTRL %s\r\n",
			prevkeycode.rctrlpressed == 1 ? "PRESSED" : "RELEASED");
		rval |= amikb_send(scancode_to_amiga(KEY_RIGHTCONTROL), prevkeycode.rctrlpressed, use_OS);
	}

	// RIGHT GUI
	if (prevkeycode.rgui != data->rgui)
	{
		prevkeycode.rgui = data->rgui;
		if (data->rgui == 1)
			prevkeycode.rguipressed = 1;
		else
			prevkeycode.rguipressed = 0;
		DBG_V("RIGHT KEYGUI %s\r\n",
			prevkeycode.rguipressed == 1 ? "PRESSED" : "RELEASED");
		rval |= amikb_send(scancode_to_amiga(KEY_RIGHT_GUI), prevkeycode.rguipressed, use_OS);
	}

	// Send all pressed key
	for (i = 0; i < KEY_PRESSED_MAX; i++)
	{
		if (prevkeycode.keys[i] != data->keys[i])
		{
			prevkeycode.keyspressed[i] = !prevkeycode.keyspressed[i];
			DBG_V("Keycode: 0x%02x -- %s\r\n", data->keys[i],
				prevkeycode.keyspressed[i] == 1 ? "PRESSED" : "RELEASED");
			if (data->keys[i] != prevkeycode.keys[i])
			{
				if (data->keys[i] == 0x00) // Previous key was released
				{
					DBG_V("Sending the KEY_RELEASE for OLD Keycode: 0x%02x\r\n",
						prevkeycode.keys[i]);
					rval |= amikb_send(scancode_to_amiga(prevkeycode.keys[i]), 0 /* Released */, use_OS);
				}
				else
				{
					DBG_V("Sending the KEY_PRESS for NEW Keycode: 0x%02x\r\n",
						data->keys[i]);
					rval |= amikb_send(scancode_to_amiga(data->keys[i]), 1 /* Pressed */, use_OS);
				}
				prevkeycode.keys[i] = data->keys[i];
			}
		}
	}

	DBG_N("Exit with rval: %d\r\n", rval);
	return rval;
}
